M1kerochip/arduino-atari-hid-keyboard/Pics/9164169800_1578827160.jpg

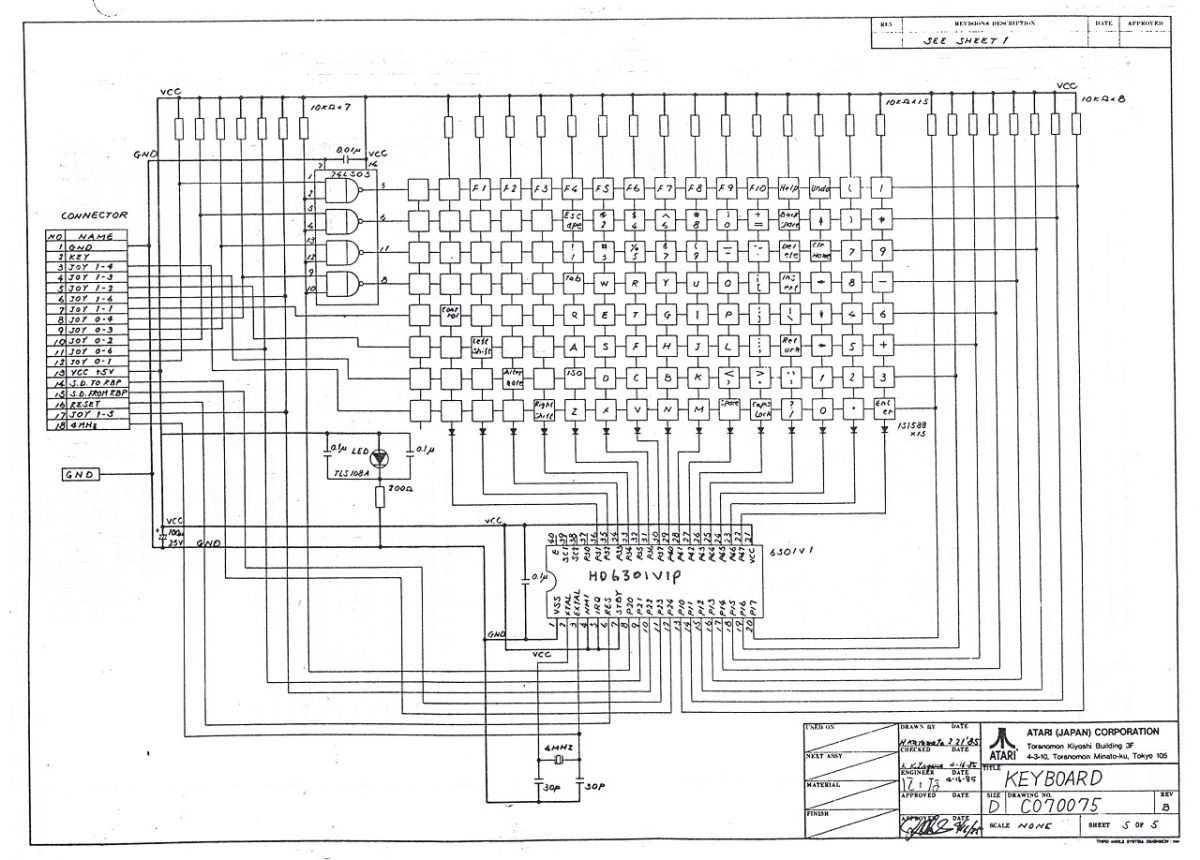
Pics/9164169800_1578827160.jpg
